joaogabrielsantosD/Dongle-eaLIVE-PCB/03_Libraries/03_3Dmodels/TJA1050T/TJA1050.step

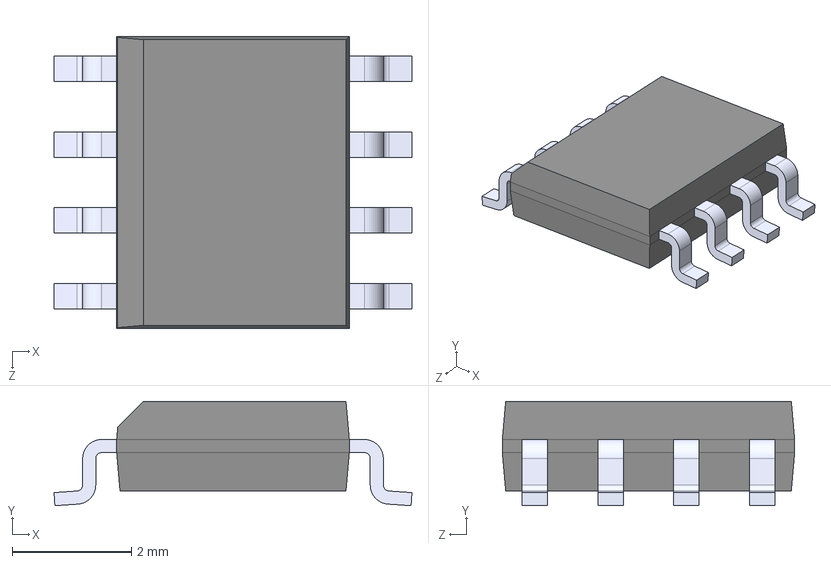
[picture p20: CAD file, 2024-09-21]
03_Libraries/03_3Dmodels/TJA1050T/TJA1050.step
6.00 x 1.75 x 4.90 mm
